jankae/LibreCAL/Software/LibreCAL/FreeRTOS-Kernel/include/task.h

/*
 * FreeRTOS Kernel <DEVELOPMENT BRANCH>
 * Copyright (C) 2021 Amazon.com, Inc. or its affiliates.  All Rights Reserved.
 *
 * SPDX-License-Identifier: MIT
 *
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
 * https://www.FreeRTOS.org
 * https://github.com/FreeRTOS
 *
 */


#ifndef INC_TASK_H
#define INC_TASK_H

#ifndef INC_FREERTOS_H
    #error "include FreeRTOS.h must appear in source files before include task.h"
#endif

#include "../../FreeRTOS-Kernel/include/list.h"

/* *INDENT-OFF* */
#ifdef __cplusplus
    extern "C" {
#endif
/* *INDENT-ON* */

/*-----------------------------------------------------------
* MACROS AND DEFINITIONS
*----------------------------------------------------------*/

/*
 * If tskKERNEL_VERSION_NUMBER ends with + it represents the version in development
 * after the numbered release.
 *
 * The tskKERNEL_VERSION_MAJOR, tskKERNEL_VERSION_MINOR, tskKERNEL_VERSION_BUILD
 * values will reflect the last released version number.
 */
#define tskKERNEL_VERSION_NUMBER       "V10.4.4+"
#define tskKERNEL_VERSION_MAJOR        10
#define tskKERNEL_VERSION_MINOR        4
#define tskKERNEL_VERSION_BUILD        4

/* MPU region parameters passed in ulParameters
 * of MemoryRegion_t struct. */
#define tskMPU_REGION_READ_ONLY        ( 1UL << 0UL )
#define tskMPU_REGION_READ_WRITE       ( 1UL << 1UL )
#define tskMPU_REGION_EXECUTE_NEVER    ( 1UL << 2UL )
#define tskMPU_REGION_NORMAL_MEMORY    ( 1UL << 3UL )
#define tskMPU_REGION_DEVICE_MEMORY    ( 1UL << 4UL )

/* The direct to task notification feature used to have only a single notification
 * per task.  Now there is an array of notifications per task that is dimensioned by
 * configTASK_NOTIFICATION_ARRAY_ENTRIES.  For backward compatibility, any use of the
 * original direct to task notification defaults to using the first index in the
 * array. */
#define tskDEFAULT_INDEX_TO_NOTIFY     ( 0 )

/**
 * task. h
 *
 * Type by which tasks are referenced.  For example, a call to xTaskCreate
 * returns (via a pointer parameter) an TaskHandle_t variable that can then
 * be used as a parameter to vTaskDelete to delete the task.
 *
 * \defgroup TaskHandle_t TaskHandle_t
 * \ingroup Tasks
 */
struct tskTaskControlBlock; /* The old naming convention is used to prevent breaking kernel aware debuggers. */
typedef struct tskTaskControlBlock * TaskHandle_t;

/*
 * Defines the prototype to which the application task hook function must
 * conform.
 */
typedef BaseType_t (* TaskHookFunction_t)( void * );

/* Task states returned by eTaskGetState. */
typedef enum
{
    eRunning = 0, /* A task is querying the state of itself, so must be running. */
    eReady,       /* The task being queried is in a ready or pending ready list. */
    eBlocked,     /* The task being queried is in the Blocked state. */
    eSuspended,   /* The task being queried is in the Suspended state, or is in the Blocked state with an infinite time out. */
    eDeleted,     /* The task being queried has been deleted, but its TCB has not yet been freed. */
    eInvalid      /* Used as an 'invalid state' value. */
} eTaskState;

/* Actions that can be performed when vTaskNotify() is called. */
typedef enum
{
    eNoAction = 0,            /* Notify the task without updating its notify value. */
    eSetBits,                 /* Set bits in the task's notification value. */
    eIncrement,               /* Increment the task's notification value. */
    eSetValueWithOverwrite,   /* Set the task's notification value to a specific value even if the previous value has not yet been read by the task. */
    eSetValueWithoutOverwrite /* Set the task's notification value if the previous value has been read by the task. */
} eNotifyAction;

/*
 * Used internally only.
 */
typedef struct xTIME_OUT
{
    BaseType_t xOverflowCount;
    TickType_t xTimeOnEntering;
} TimeOut_t;

/*
 * Defines the memory ranges allocated to the task when an MPU is used.
 */
typedef struct xMEMORY_REGION
{
    void * pvBaseAddress;
    uint32_t ulLengthInBytes;
    uint32_t ulParameters;
} MemoryRegion_t;

/*
 * Parameters required to create an MPU protected task.
 */
typedef struct xTASK_PARAMETERS
{
    TaskFunction_t pvTaskCode;
    const char * pcName; /*lint !e971 Unqualified char types are allowed for strings and single characters only. */
    configSTACK_DEPTH_TYPE usStackDepth;
    void * pvParameters;
    UBaseType_t uxPriority;
    StackType_t * puxStackBuffer;
    MemoryRegion_t xRegions[ portNUM_CONFIGURABLE_REGIONS ];
    #if ( ( portUSING_MPU_WRAPPERS == 1 ) && ( configSUPPORT_STATIC_ALLOCATION == 1 ) )
        StaticTask_t * const pxTaskBuffer;
    #endif
} TaskParameters_t;

/* Used with the uxTaskGetSystemState() function to return the state of each task
 * in the system. */
typedef struct xTASK_STATUS
{
    TaskHandle_t xHandle;                         /* The handle of the task to which the rest of the information in the structure relates. */
    const char * pcTaskName;                      /* A pointer to the task's name.  This value will be invalid if the task was deleted since the structure was populated! */ /*lint !e971 Unqualified char types are allowed for strings and single characters only. */
    UBaseType_t xTaskNumber;                      /* A number unique to the task. */
    eTaskState eCurrentState;                     /* The state in which the task existed when the structure was populated. */
    UBaseType_t uxCurrentPriority;                /* The priority at which the task was running (may be inherited) when the structure was populated. */
    UBaseType_t uxBasePriority;                   /* The priority to which the task will return if the task's current priority has been inherited to avoid unbounded priority inversion when obtaining a mutex.  Only valid if configUSE_MUTEXES is defined as 1 in FreeRTOSConfig.h. */
    configRUN_TIME_COUNTER_TYPE ulRunTimeCounter; /* The total run time allocated to the task so far, as defined by the run time stats clock.  See https://www.FreeRTOS.org/rtos-run-time-stats.html.  Only valid when configGENERATE_RUN_TIME_STATS is defined as 1 in FreeRTOSConfig.h. */
    StackType_t * pxStackBase;                    /* Points to the lowest address of the task's stack area. */
    #if ( ( portSTACK_GROWTH > 0 ) && ( configRECORD_STACK_HIGH_ADDRESS == 1 ) )
        StackType_t * pxTopOfStack;               /* Points to the top address of the task's stack area. */
        StackType_t * pxEndOfStack;               /* Points to the end address of the task's stack area. */
    #endif
    configSTACK_DEPTH_TYPE usStackHighWaterMark;  /* The minimum amount of stack space that has remained for the task since the task was created.  The closer this value is to zero the closer the task has come to overflowing its stack. */
} TaskStatus_t;

/* Possible return values for eTaskConfirmSleepModeStatus(). */
typedef enum
{
    eAbortSleep = 0,           /* A task has been made ready or a context switch pended since portSUPPRESS_TICKS_AND_SLEEP() was called - abort entering a sleep mode. */
    eStandardSleep,            /* Enter a sleep mode that will not last any longer than the expected idle time. */
    #if ( INCLUDE_vTaskSuspend == 1 )
        eNoTasksWaitingTimeout /* No tasks are waiting for a timeout so it is safe to enter a sleep mode that can only be exited by an external interrupt. */
    #endif /* INCLUDE_vTaskSuspend */
} eSleepModeStatus;

/**
 * Defines the priority used by the idle task.  This must not be modified.
 *
 * \ingroup TaskUtils
 */
#define tskIDLE_PRIORITY    ( ( UBaseType_t ) 0U )

/**
 * task. h
 *
 * Macro for forcing a context switch.
 *
 * \defgroup taskYIELD taskYIELD
 * \ingroup SchedulerControl
 */
#define taskYIELD()                        portYIELD()

/**
 * task. h
 *
 * Macro to mark the start of a critical code region.  Preemptive context
 * switches cannot occur when in a critical region.
 *
 * NOTE: This may alter the stack (depending on the portable implementation)
 * so must be used with care!
 *
 * \defgroup taskENTER_CRITICAL taskENTER_CRITICAL
 * \ingroup SchedulerControl
 */
#define taskENTER_CRITICAL()               portENTER_CRITICAL()
#define taskENTER_CRITICAL_FROM_ISR()      portSET_INTERRUPT_MASK_FROM_ISR()

/**
 * task. h
 *
 * Macro to mark the end of a critical code region.  Preemptive context
 * switches cannot occur when in a critical region.
 *
 * NOTE: This may alter the stack (depending on the portable implementation)
 * so must be used with care!
 *
 * \defgroup taskEXIT_CRITICAL taskEXIT_CRITICAL
 * \ingroup SchedulerControl
 */
#define taskEXIT_CRITICAL()                portEXIT_CRITICAL()
#define taskEXIT_CRITICAL_FROM_ISR( x )    portCLEAR_INTERRUPT_MASK_FROM_ISR( x )

/**
 * task. h
 *
 * Macro to disable all maskable interrupts.
 *
 * \defgroup taskDISABLE_INTERRUPTS taskDISABLE_INTERRUPTS
 * \ingroup SchedulerControl
 */
#define taskDISABLE_INTERRUPTS()           portDISABLE_INTERRUPTS()

/**
 * task. h
 *
 * Macro to enable microcontroller interrupts.
 *
 * \defgroup taskENABLE_INTERRUPTS taskENABLE_INTERRUPTS
 * \ingroup SchedulerControl
 */
#define taskENABLE_INTERRUPTS()            portENABLE_INTERRUPTS()

/* Definitions returned by xTaskGetSchedulerState().  taskSCHEDULER_SUSPENDED is
 * 0 to generate more optimal code when configASSERT() is defined as the constant
 * is used in assert() statements. */
#define taskSCHEDULER_SUSPENDED      ( ( BaseType_t ) 0 )
#define taskSCHEDULER_NOT_STARTED    ( ( BaseType_t ) 1 )
#define taskSCHEDULER_RUNNING        ( ( BaseType_t ) 2 )


/*-----------------------------------------------------------
* TASK CREATION API
*----------------------------------------------------------*/

/**
 * task. h
 * @code{c}
 * BaseType_t xTaskCreate(
 *                            TaskFunction_t pxTaskCode,
 *                            const char *pcName,
 *                            configSTACK_DEPTH_TYPE usStackDepth,
 *                            void *pvParameters,
 *                            UBaseType_t uxPriority,
 *                            TaskHandle_t *pxCreatedTask
 *                        );
 * @endcode
 *
 * Create a new task and add it to the list of tasks that are ready to run.
 *
 * Internally, within the FreeRTOS implementation, tasks use two blocks of
 * memory.  The first block is used to hold the task's data structures.  The
 * second block is used by the task as its stack.  If a task is created using
 * xTaskCreate() then both blocks of memory are automatically dynamically
 * allocated inside the xTaskCreate() function.  (see
 * https://www.FreeRTOS.org/a00111.html).  If a task is created using
 * xTaskCreateStatic() then the application writer must provide the required
 * memory.  xTaskCreateStatic() therefore allows a task to be created without
 * using any dynamic memory allocation.
 *
 * See xTaskCreateStatic() for a version that does not use any dynamic memory
 * allocation.
 *
 * xTaskCreate() can only be used to create a task that has unrestricted
 * access to the entire microcontroller memory map.  Systems that include MPU
 * support can alternatively create an MPU constrained task using
 * xTaskCreateRestricted().
 *
 * @param pxTaskCode Pointer to the task entry function.  Tasks
 * must be implemented to never return (i.e. continuous loop).
 *
 * @param pcName A descriptive name for the task.  This is mainly used to
 * facilitate debugging.  Max length defined by configMAX_TASK_NAME_LEN - default
 * is 16.
 *
 * @param usStackDepth The size of the task stack specified as the number of
 * variables the stack can hold - not the number of bytes.  For example, if
 * the stack is 16 bits wide and usStackDepth is defined as 100, 200 bytes
 * will be allocated for stack storage.
 *
 * @param pvParameters Pointer that will be used as the parameter for the task
 * being created.
 *
 * @param uxPriority The priority at which the task should run.  Systems that
 * include MPU support can optionally create tasks in a privileged (system)
 * mode by setting bit portPRIVILEGE_BIT of the priority parameter.  For
 * example, to create a privileged task at priority 2 the uxPriority parameter
 * should be set to ( 2 | portPRIVILEGE_BIT ).
 *
 * @param pxCreatedTask Used to pass back a handle by which the created task
 * can be referenced.
 *
 * @return pdPASS if the task was successfully created and added to a ready
 * list, otherwise an error code defined in the file projdefs.h
 *
 * Example usage:
 * @code{c}
 * // Task to be created.
 * void vTaskCode( void * pvParameters )
 * {
 *   for( ;; )
 *   {
 *       // Task code goes here.
 *   }
 * }
 *
 * // Function that creates a task.
 * void vOtherFunction( void )
 * {
 * static uint8_t ucParameterToPass;
 * TaskHandle_t xHandle = NULL;
 *
 *   // Create the task, storing the handle.  Note that the passed parameter ucParameterToPass
 *   // must exist for the lifetime of the task, so in this case is declared static.  If it was just an
 *   // an automatic stack variable it might no longer exist, or at least have been corrupted, by the time
 *   // the new task attempts to access it.
 *   xTaskCreate( vTaskCode, "NAME", STACK_SIZE, &ucParameterToPass, tskIDLE_PRIORITY, &xHandle );
 *   configASSERT( xHandle );
 *
 *   // Use the handle to delete the task.
 *   if( xHandle != NULL )
 *   {
 *      vTaskDelete( xHandle );
 *   }
 * }
 * @endcode
 * \defgroup xTaskCreate xTaskCreate
 * \ingroup Tasks
 */
#if ( configSUPPORT_DYNAMIC_ALLOCATION == 1 )
    BaseType_t xTaskCreate( TaskFunction_t pxTaskCode,
                            const char * const pcName, /*lint !e971 Unqualified char types are allowed for strings and single characters only. */
                            const configSTACK_DEPTH_TYPE usStackDepth,
                            void * const pvParameters,
                            UBaseType_t uxPriority,
                            TaskHandle_t * const pxCreatedTask ) PRIVILEGED_FUNCTION;
#endif

/**
 * task. h
 * @code{c}
 * TaskHandle_t xTaskCreateStatic( TaskFunction_t pxTaskCode,
 *                               const char *pcName,
 *                               uint32_t ulStackDepth,
 *                               void *pvParameters,
 *                               UBaseType_t uxPriority,
 *                               StackType_t *puxStackBuffer,
 *                               StaticTask_t *pxTaskBuffer );
 * @endcode
 *
 * Create a new task and add it to the list of tasks that are ready to run.
 *
 * Internally, within the FreeRTOS implementation, tasks use two blocks of
 * memory.  The first block is used to hold the task's data structures.  The
 * second block is used by the task as its stack.  If a task is created using
 * xTaskCreate() then both blocks of memory are automatically dynamically
 * allocated inside the xTaskCreate() function.  (see
 * https://www.FreeRTOS.org/a00111.html).  If a task is created using
 * xTaskCreateStatic() then the application writer must provide the required
 * memory.  xTaskCreateStatic() therefore allows a task to be created without
 * using any dynamic memory allocation.
 *
 * @param pxTaskCode Pointer to the task entry function.  Tasks
 * must be implemented to never return (i.e. continuous loop).
 *
 * @param pcName A descriptive name for the task.  This is mainly used to
 * facilitate debugging.  The maximum length of the string is defined by
 * configMAX_TASK_NAME_LEN in FreeRTOSConfig.h.
 *
 * @param ulStackDepth The size of the task stack specified as the number of
 * variables the stack can hold - not the number of bytes.  For example, if
 * the stack is 32-bits wide and ulStackDepth is defined as 100 then 400 bytes
 * will be allocated for stack storage.
 *
 * @param pvParameters Pointer that will be used as the parameter for the task
 * being created.
 *
 * @param uxPriority The priority at which the task will run.
 *
 * @param puxStackBuffer Must point to a StackType_t array that has at least
 * ulStackDepth indexes - the array will then be used as the task's stack,
 * removing the need for the stack to be allocated dynamically.
 *
 * @param pxTaskBuffer Must point to a variable of type StaticTask_t, which will
 * then be used to hold the task's data structures, removing the need for the
 * memory to be allocated dynamically.
 *
 * @return If neither puxStackBuffer nor pxTaskBuffer are NULL, then the task
 * will be created and a handle to the created task is returned.  If either
 * puxStackBuffer or pxTaskBuffer are NULL then the task will not be created and
 * NULL is returned.
 *
 * Example usage:
 * @code{c}
 *
 *  // Dimensions of the buffer that the task being created will use as its stack.
 *  // NOTE:  This is the number of words the stack will hold, not the number of
 *  // bytes.  For example, if each stack item is 32-bits, and this is set to 100,
 *  // then 400 bytes (100 * 32-bits) will be allocated.
 #define STACK_SIZE 200
 *
 *  // Structure that will hold the TCB of the task being created.
 *  StaticTask_t xTaskBuffer;
 *
 *  // Buffer that the task being created will use as its stack.  Note this is
 *  // an array of StackType_t variables.  The size of StackType_t is dependent on
 *  // the RTOS port.
 *  StackType_t xStack[ STACK_SIZE ];
 *
 *  // Function that implements the task being created.
 *  void vTaskCode( void * pvParameters )
 *  {
 *      // The parameter value is expected to be 1 as 1 is passed in the
 *      // pvParameters value in the call to xTaskCreateStatic().
 *      configASSERT( ( uint32_t ) pvParameters == 1UL );
 *
 *      for( ;; )
 *      {
 *          // Task code goes here.
 *      }
 *  }
 *
 *  // Function that creates a task.
 *  void vOtherFunction( void )
 *  {
 *      TaskHandle_t xHandle = NULL;
 *
 *      // Create the task without using any dynamic memory allocation.
 *      xHandle = xTaskCreateStatic(
 *                    vTaskCode,       // Function that implements the task.
 *                    "NAME",          // Text name for the task.
 *                    STACK_SIZE,      // Stack size in words, not bytes.
 *                    ( void * ) 1,    // Parameter passed into the task.
 *                    tskIDLE_PRIORITY,// Priority at which the task is created.
 *                    xStack,          // Array to use as the task's stack.
 *                    &xTaskBuffer );  // Variable to hold the task's data structure.
 *
 *      // puxStackBuffer and pxTaskBuffer were not NULL, so the task will have
 *      // been created, and xHandle will be the task's handle.  Use the handle
 *      // to suspend the task.
 *      vTaskSuspend( xHandle );
 *  }
 * @endcode
 * \defgroup xTaskCreateStatic xTaskCreateStatic
 * \ingroup Tasks
 */
#if ( configSUPPORT_STATIC_ALLOCATION == 1 )
    TaskHandle_t xTaskCreateStatic( TaskFunction_t pxTaskCode,
                                    const char * const pcName, /*lint !e971 Unqualified char types are allowed for strings and single characters only. */
                                    const uint32_t ulStackDepth,
                                    void * const pvParameters,
                                    UBaseType_t uxPriority,
                                    StackType_t * const puxStackBuffer,
                                    StaticTask_t * const pxTaskBuffer ) PRIVILEGED_FUNCTION;
#endif /* configSUPPORT_STATIC_ALLOCATION */

/**
 * task. h
 * @code{c}
 * BaseType_t xTaskCreateRestricted( TaskParameters_t *pxTaskDefinition, TaskHandle_t *pxCreatedTask );
 * @endcode
 *
 * Only available when configSUPPORT_DYNAMIC_ALLOCATION is set to 1.
 *
 * xTaskCreateRestricted() should only be used in systems that include an MPU
 * implementation.
 *
 * Create a new task and add it to the list of tasks that are ready to run.
 * The function parameters define the memory regions and associated access
 * permissions allocated to the task.
 *
 * See xTaskCreateRestrictedStatic() for a version that does not use any
 * dynamic memory allocation.
 *
 * @param pxTaskDefinition Pointer to a structure that contains a member
 * for each of the normal xTaskCreate() parameters (see the xTaskCreate() API
 * documentation) plus an optional stack buffer and the memory region
 * definitions.
 *
 * @param pxCreatedTask Used to pass back a handle by which the created task
 * can be referenced.
 *
 * @return pdPASS if the task was successfully created and added to a ready
 * list, otherwise an error code defined in the file projdefs.h
 *
 * Example usage:
 * @code{c}
 * // Create an TaskParameters_t structure that defines the task to be created.
 * static const TaskParameters_t xCheckTaskParameters =
 * {
 *  vATask,     // pvTaskCode - the function that implements the task.
 *  "ATask",    // pcName - just a text name for the task to assist debugging.
 *  100,        // usStackDepth - the stack size DEFINED IN WORDS.
 *  NULL,       // pvParameters - passed into the task function as the function parameters.
 *  ( 1UL | portPRIVILEGE_BIT ),// uxPriority - task priority, set the portPRIVILEGE_BIT if the task should run in a privileged state.
 *  cStackBuffer,// puxStackBuffer - the buffer to be used as the task stack.
 *
 *  // xRegions - Allocate up to three separate memory regions for access by
 *  // the task, with appropriate access permissions.  Different processors have
 *  // different memory alignment requirements - refer to the FreeRTOS documentation
 *  // for full information.
 *  {
 *      // Base address                 Length  Parameters
 *      { cReadWriteArray,              32,     portMPU_REGION_READ_WRITE },
 *      { cReadOnlyArray,               32,     portMPU_REGION_READ_ONLY },
 *      { cPrivilegedOnlyAccessArray,   128,    portMPU_REGION_PRIVILEGED_READ_WRITE }
 *  }
 * };
 *
 * int main( void )
 * {
 * TaskHandle_t xHandle;
 *
 *  // Create a task from the const structure defined above.  The task handle
 *  // is requested (the second parameter is not NULL) but in this case just for
 *  // demonstration purposes as its not actually used.
 *  xTaskCreateRestricted( &xRegTest1Parameters, &xHandle );
 *
 *  // Start the scheduler.
 *  vTaskStartScheduler();
 *
 *  // Will only get here if there was insufficient memory to create the idle
 *  // and/or timer task.
 *  for( ;; );
 * }
 * @endcode
 * \defgroup xTaskCreateRestricted xTaskCreateRestricted
 * \ingroup Tasks
 */
#if ( portUSING_MPU_WRAPPERS == 1 )
    BaseType_t xTaskCreateRestricted( const TaskParameters_t * const pxTaskDefinition,
                                      TaskHandle_t * pxCreatedTask ) PRIVILEGED_FUNCTION;
#endif

/**
 * task. h
 * @code{c}
 * BaseType_t xTaskCreateRestrictedStatic( TaskParameters_t *pxTaskDefinition, TaskHandle_t *pxCreatedTask );
 * @endcode
 *
 * Only available when configSUPPORT_STATIC_ALLOCATION is set to 1.
 *
 * xTaskCreateRestrictedStatic() should only be used in systems that include an
 * MPU implementation.
 *
 * Internally, within the FreeRTOS implementation, tasks use two blocks of
 * memory.  The first block is used to hold the task's data structures.  The
 * second block is used by the task as its stack.  If a task is created using
 * xTaskCreateRestricted() then the stack is provided by the application writer,
 * and the memory used to hold the task's data structure is automatically
 * dynamically allocated inside the xTaskCreateRestricted() function.  If a task
 * is created using xTaskCreateRestrictedStatic() then the application writer
 * must provide the memory used to hold the task's data structures too.
 * xTaskCreateRestrictedStatic() therefore allows a memory protected task to be
 * created without using any dynamic memory allocation.
 *
 * @param pxTaskDefinition Pointer to a structure that contains a member
 * for each of the normal xTaskCreate() parameters (see the xTaskCreate() API
 * documentation) plus an optional stack buffer and the memory region
 * definitions.  If configSUPPORT_STATIC_ALLOCATION is set to 1 the structure
 * contains an additional member, which is used to point to a variable of type
 * StaticTask_t - which is then used to hold the task's data structure.
 *
 * @param pxCreatedTask Used to pass back a handle by which the created task
 * can be referenced.
 *
 * @return pdPASS if the task was successfully created and added to a ready
 * list, otherwise an error code defined in the file projdefs.h
 *
 * Example usage:
 * @code{c}
 * // Create an TaskParameters_t structure that defines the task to be created.
 * // The StaticTask_t variable is only included in the structure when
 * // configSUPPORT_STATIC_ALLOCATION is set to 1.  The PRIVILEGED_DATA macro can
 * // be used to force the variable into the RTOS kernel's privileged data area.
 * static PRIVILEGED_DATA StaticTask_t xTaskBuffer;
 * static const TaskParameters_t xCheckTaskParameters =
 * {
 *  vATask,     // pvTaskCode - the function that implements the task.
 *  "ATask",    // pcName - just a text name for the task to assist debugging.
 *  100,        // usStackDepth - the stack size DEFINED IN WORDS.
 *  NULL,       // pvParameters - passed into the task function as the function parameters.
 *  ( 1UL | portPRIVILEGE_BIT ),// uxPriority - task priority, set the portPRIVILEGE_BIT if the task should run in a privileged state.
 *  cStackBuffer,// puxStackBuffer - the buffer to be used as the task stack.
 *
 *  // xRegions - Allocate up to three separate memory regions for access by
 *  // the task, with appropriate access permissions.  Different processors have
 *  // different memory alignment requirements - refer to the FreeRTOS documentation
 *  // for full information.
 *  {
 *      // Base address                 Length  Parameters
 *      { cReadWriteArray,              32,     portMPU_REGION_READ_WRITE },
 *      { cReadOnlyArray,               32,     portMPU_REGION_READ_ONLY },
 *      { cPrivilegedOnlyAccessArray,   128,    portMPU_REGION_PRIVILEGED_READ_WRITE }
 *  }
 *
 *  &xTaskBuffer; // Holds the task's data structure.
 * };
 *
 * int main( void )
 * {
 * TaskHandle_t xHandle;
 *
 *  // Create a task from the const structure defined above.  The task handle
 *  // is requested (the second parameter is not NULL) but in this case just for
 *  // demonstration purposes as its not actually used.
 *  xTaskCreateRestricted( &xRegTest1Parameters, &xHandle );
 *
 *  // Start the scheduler.
 *  vTaskStartScheduler();
 *
 *  // Will only get here if there was insufficient memory to create the idle
 *  // and/or timer task.
 *  for( ;; );
 * }
 * @endcode
 * \defgroup xTaskCreateRestrictedStatic xTaskCreateRestrictedStatic
 * \ingroup Tasks
 */
#if ( ( portUSING_MPU_WRAPPERS == 1 ) && ( configSUPPORT_STATIC_ALLOCATION == 1 ) )
    BaseType_t xTaskCreateRestrictedStatic( const TaskParameters_t * const pxTaskDefinition,
                                            TaskHandle_t * pxCreatedTask ) PRIVILEGED_FUNCTION;
#endif

/**
 * task. h
 * @code{c}
 * void vTaskAllocateMPURegions( TaskHandle_t xTask, const MemoryRegion_t * const pxRegions );
 * @endcode
 *
 * Memory regions are assigned to a restricted task when the task is created by
 * a call to xTaskCreateRestricted().  These regions can be redefined using
 * vTaskAllocateMPURegions().
 *
 * @param xTask The handle of the task being updated.
 *
 * @param xRegions A pointer to a MemoryRegion_t structure that contains the
 * new memory region definitions.
 *
 * Example usage:
 * @code{c}
 * // Define an array of MemoryRegion_t structures that configures an MPU region
 * // allowing read/write access for 1024 bytes starting at the beginning of the
 * // ucOneKByte array.  The other two of the maximum 3 definable regions are
 * // unused so set to zero.
 * static const MemoryRegion_t xAltRegions[ portNUM_CONFIGURABLE_REGIONS ] =
 * {
 *  // Base address     Length      Parameters
 *  { ucOneKByte,       1024,       portMPU_REGION_READ_WRITE },
 *  { 0,                0,          0 },
 *  { 0,                0,          0 }
 * };
 *
 * void vATask( void *pvParameters )
 * {
 *  // This task was created such that it has access to certain regions of
 *  // memory as defined by the MPU configuration.  At some point it is
 *  // desired that these MPU regions are replaced with that defined in the
 *  // xAltRegions const struct above.  Use a call to vTaskAllocateMPURegions()
 *  // for this purpose.  NULL is used as the task handle to indicate that this
 *  // function should modify the MPU regions of the calling task.
 *  vTaskAllocateMPURegions( NULL, xAltRegions );
 *
 *  // Now the task can continue its function, but from this point on can only
 *  // access its stack and the ucOneKByte array (unless any other statically
 *  // defined or shared regions have been declared elsewhere).
 * }
 * @endcode
 * \defgroup xTaskCreateRestricted xTaskCreateRestricted
 * \ingroup Tasks
 */
void vTaskAllocateMPURegions( TaskHandle_t xTask,
                              const MemoryRegion_t * const pxRegions ) PRIVILEGED_FUNCTION;

/**
 * task. h
 * @code{c}
 * void vTaskDelete( TaskHandle_t xTaskToDelete );
 * @endcode
 *
 * INCLUDE_vTaskDelete must be defined as 1 for this function to be available.
 * See the configuration section for more information.
 *
 * Remove a task from the RTOS real time kernel's management.  The task being
 * deleted will be removed from all ready, blocked, suspended and event lists.
 *
 * NOTE:  The idle task is responsible for freeing the kernel allocated
 * memory from tasks that have been deleted.  It is therefore important that
 * the idle task is not starved of microcontroller processing time if your
 * application makes any calls to vTaskDelete ().  Memory allocated by the
 * task code is not automatically freed, and should be freed before the task
 * is deleted.
 *
 * See the demo application file death.c for sample code that utilises
 * vTaskDelete ().
 *
 * @param xTaskToDelete The handle of the task to be deleted.  Passing NULL will
 * cause the calling task to be deleted.
 *
 * Example usage:
 * @code{c}
 * void vOtherFunction( void )
 * {
 * TaskHandle_t xHandle;
 *
 *   // Create the task, storing the handle.
 *   xTaskCreate( vTaskCode, "NAME", STACK_SIZE, NULL, tskIDLE_PRIORITY, &xHandle );
 *
 *   // Use the handle to delete the task.
 *   vTaskDelete( xHandle );
 * }
 * @endcode
 * \defgroup vTaskDelete vTaskDelete
 * \ingroup Tasks
 */
void vTaskDelete( TaskHandle_t xTaskToDelete ) PRIVILEGED_FUNCTION;

/*-----------------------------------------------------------
* TASK CONTROL API
*----------------------------------------------------------*/

/**
 * task. h
 * @code{c}
 * void vTaskDelay( const TickType_t xTicksToDelay );
 * @endcode
 *
 * Delay a task for a given number of ticks.  The actual time that the
 * task remains blocked depends on the tick rate.  The constant
 * portTICK_PERIOD_MS can be used to calculate real time from the tick
 * rate - with the resolution of one tick period.
 *
 * INCLUDE_vTaskDelay must be defined as 1 for this function to be available.
 * See the configuration section for more information.
 *
 *
 * vTaskDelay() specifies a time at which the task wishes to unblock relative to
 * the time at which vTaskDelay() is called.  For example, specifying a block
 * period of 100 ticks will cause the task to unblock 100 ticks after
 * vTaskDelay() is called.  vTaskDelay() does not therefore provide a good method
 * of controlling the frequency of a periodic task as the path taken through the
 * code, as well as other task and interrupt activity, will affect the frequency
 * at which vTaskDelay() gets called and therefore the time at which the task
 * next executes.  See xTaskDelayUntil() for an alternative API function designed
 * to facilitate fixed frequency execution.  It does this by specifying an
 * absolute time (rather than a relative time) at which the calling task should
 * unblock.
 *
 * @param xTicksToDelay The amount of time, in tick periods, that
 * the calling task should block.
 *
 * Example usage:
 *
 * void vTaskFunction( void * pvParameters )
 * {
 * // Block for 500ms.
 * const TickType_t xDelay = 500 / portTICK_PERIOD_MS;
 *
 *   for( ;; )
 *   {
 *       // Simply toggle the LED every 500ms, blocking between each toggle.
 *       vToggleLED();
 *       vTaskDelay( xDelay );
 *   }
 * }
 *
 * \defgroup vTaskDelay vTaskDelay
 * \ingroup TaskCtrl
 */
void vTaskDelay( const TickType_t xTicksToDelay ) PRIVILEGED_FUNCTION;

/**
 * task. h
 * @code{c}
 * BaseType_t xTaskDelayUntil( TickType_t *pxPreviousWakeTime, const TickType_t xTimeIncrement );
 * @endcode
 *
 * INCLUDE_xTaskDelayUntil must be defined as 1 for this function to be available.
 * See the configuration section for more information.
 *
 * Delay a task until a specified time.  This function can be used by periodic
 * tasks to ensure a constant execution frequency.
 *
 * This function differs from vTaskDelay () in one important aspect:  vTaskDelay () will
 * cause a task to block for the specified number of ticks from the time vTaskDelay () is
 * called.  It is therefore difficult to use vTaskDelay () by itself to generate a fixed
 * execution frequency as the time between a task starting to execute and that task
 * calling vTaskDelay () may not be fixed [the task may take a different path though the
 * code between calls, or may get interrupted or preempted a different number of times
 * each time it executes].
 *
 * Whereas vTaskDelay () specifies a wake time relative to the time at which the function
 * is called, xTaskDelayUntil () specifies the absolute (exact) time at which it wishes to
 * unblock.
 *
 * The macro pdMS_TO_TICKS() can be used to calculate the number of ticks from a
 * time specified in milliseconds with a resolution of one tick period.
 *
 * @param pxPreviousWakeTime Pointer to a variable that holds the time at which the
 * task was last unblocked.  The variable must be initialised with the current time
 * prior to its first use (see the example below).  Following this the variable is
 * automatically updated within xTaskDelayUntil ().
 *
 * @param xTimeIncrement The cycle time period.  The task will be unblocked at
 * time *pxPreviousWakeTime + xTimeIncrement.  Calling xTaskDelayUntil with the
 * same xTimeIncrement parameter value will cause the task to execute with
 * a fixed interface period.
 *
 * @return Value which can be used to check whether the task was actually delayed.
 * Will be pdTRUE if the task way delayed and pdFALSE otherwise.  A task will not
 * be delayed if the next expected wake time is in the past.
 *
 * Example usage:
 * @code{c}
 * // Perform an action every 10 ticks.
 * void vTaskFunction( void * pvParameters )
 * {
 * TickType_t xLastWakeTime;
 * const TickType_t xFrequency = 10;
 * BaseType_t xWasDelayed;
 *
 *     // Initialise the xLastWakeTime variable with the current time.
 *     xLastWakeTime = xTaskGetTickCount ();
 *     for( ;; )
 *     {
 *         // Wait for the next cycle.
 *         xWasDelayed = xTaskDelayUntil( &xLastWakeTime, xFrequency );
 *
 *         // Perform action here. xWasDelayed value can be used to determine
 *         // whether a deadline was missed if the code here took too long.
 *     }
 * }
 * @endcode
 * \defgroup xTaskDelayUntil xTaskDelayUntil
 * \ingroup TaskCtrl
 */
BaseType_t xTaskDelayUntil( TickType_t * const pxPreviousWakeTime,
                            const TickType_t xTimeIncrement ) PRIVILEGED_FUNCTION;
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
